mohamedleithy/Plant-Monitioring-Embedded-System/docs/images/ESP32.PNG

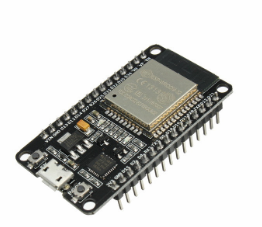
docs/images/ESP32.PNG
