mohamedleithy/Plant-Monitioring-Embedded-System/docs/images/flowers.png

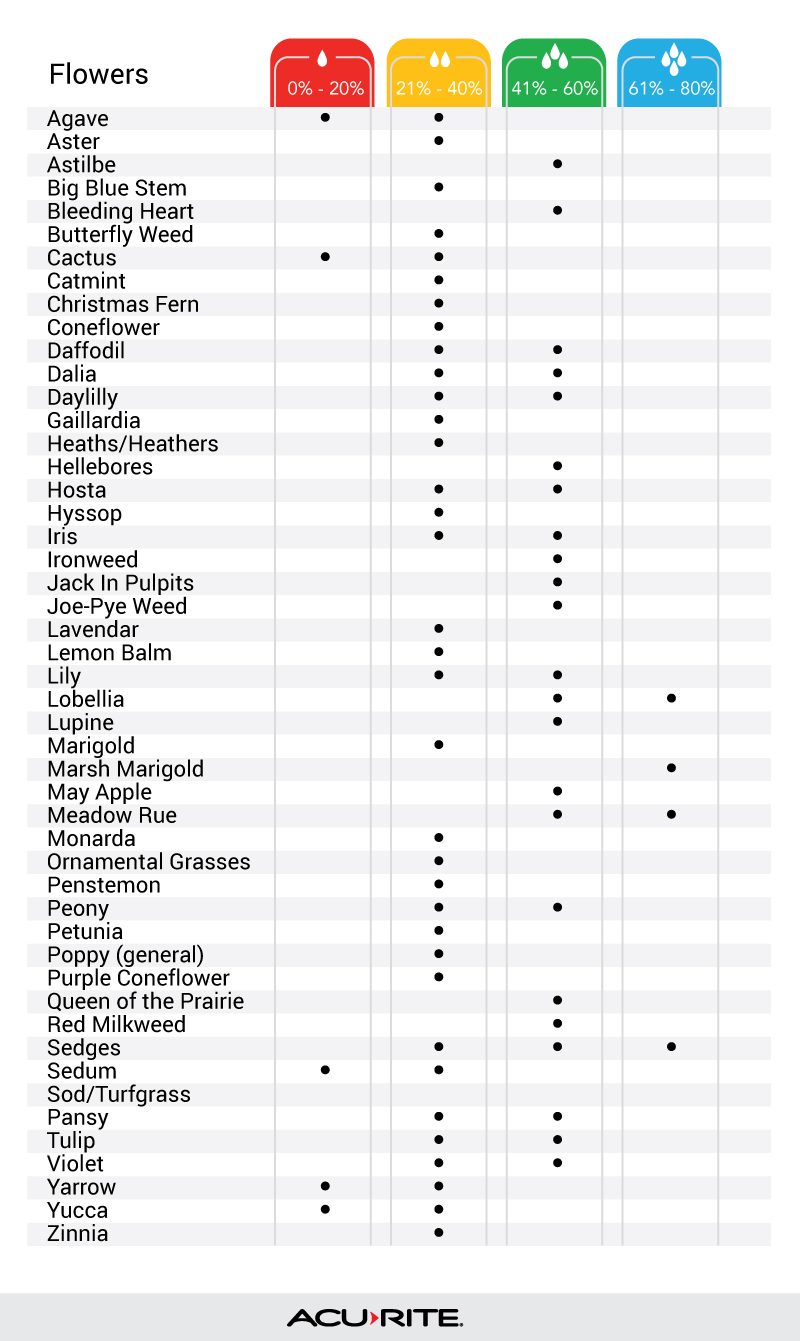
docs/images/flowers.png
